yashsethu/PlaStick/CAD/Full Assembly - Part 1 (30).step

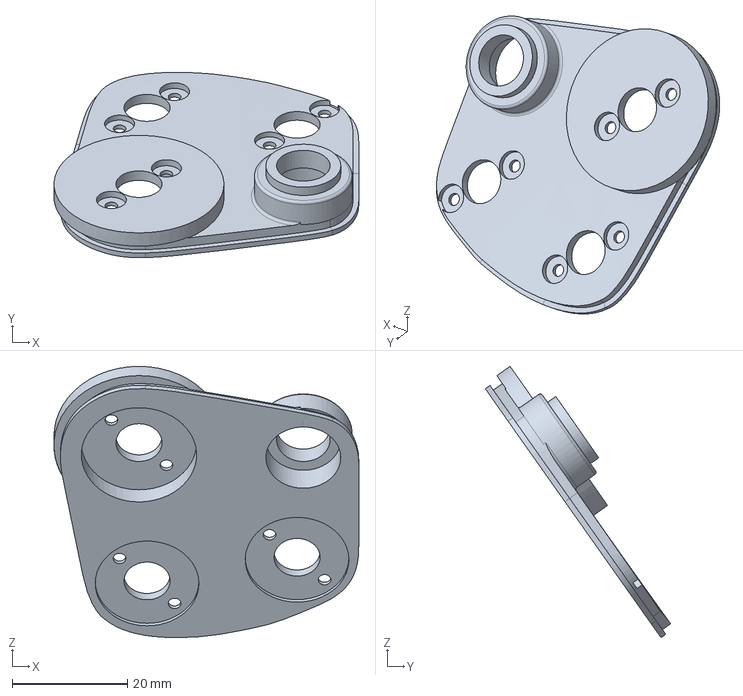
[picture p14: CAD file, 2025-06-24]
CAD/Full Assembly - Part 1 (30).step
52.9 x 32.2 x 47.1 mm
