yashsethu/PlaStick/CAD/Full Assembly - Part 1.step

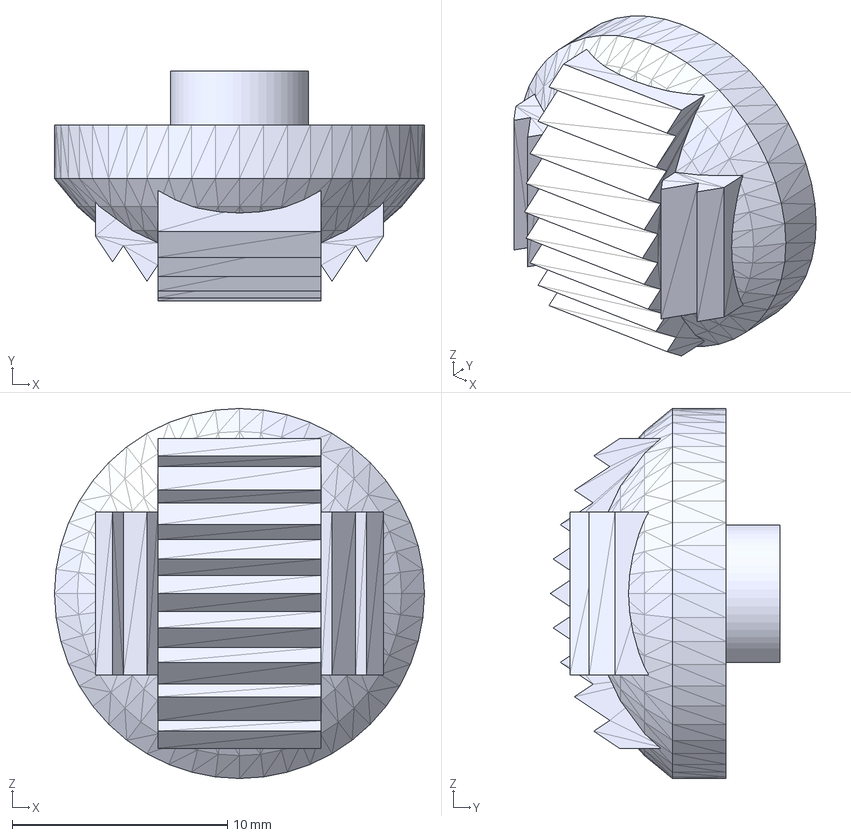
[picture p15: CAD file, 2025-06-24]
CAD/Full Assembly - Part 1.step
17.2 x 10.7 x 17.2 mm
