yashsethu/PlaStick/CAD/Full Assembly - p  BEARING, METRIC 600 MINIATURE SERIES, DOUBLE-SHIELDED  5mm ID × 11 OD × 3 W  —  685-ZZ.step

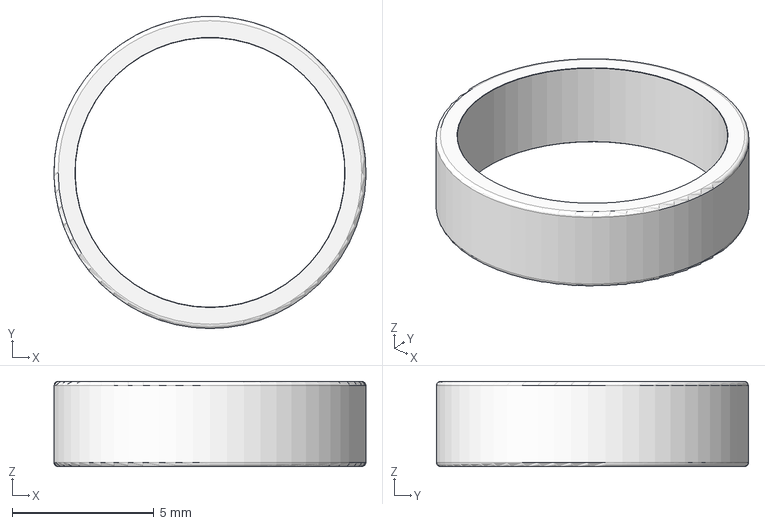
[picture p16: CAD file, 2025-06-24]
CAD/Full Assembly - p BEARING, METRIC 600 MINIATURE SERIES, DOUBLE-SHIELDED 5mm ID × 11 OD × 3 W — 685-ZZ.step
11.0 x 11.0 x 3.00 mm
