yashsethu/PlaStick/CAD/Full Assembly - Part 1 (26).step

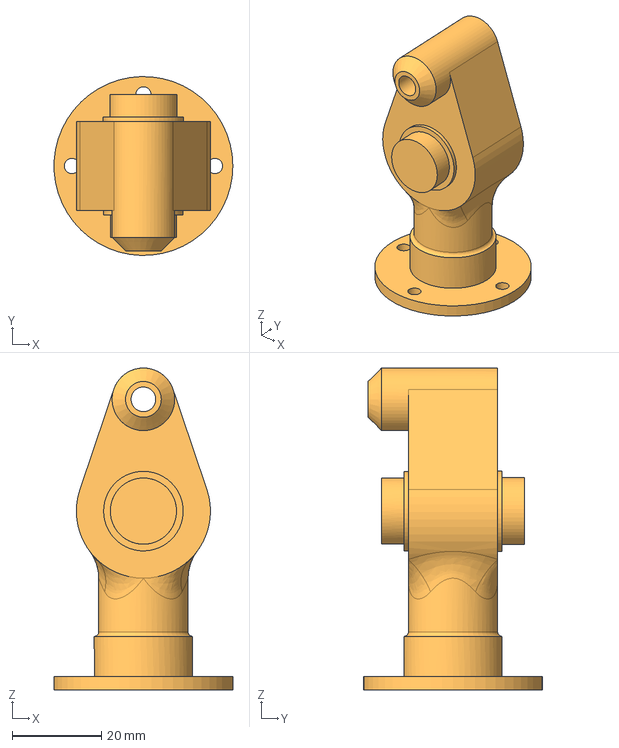
[picture p17: CAD file, 2025-06-24]
CAD/Full Assembly - Part 1 (26).step
40.0 x 40.0 x 72.0 mm
