yashsethu/PlaStick/CAD/Full Assembly - Part 6.step

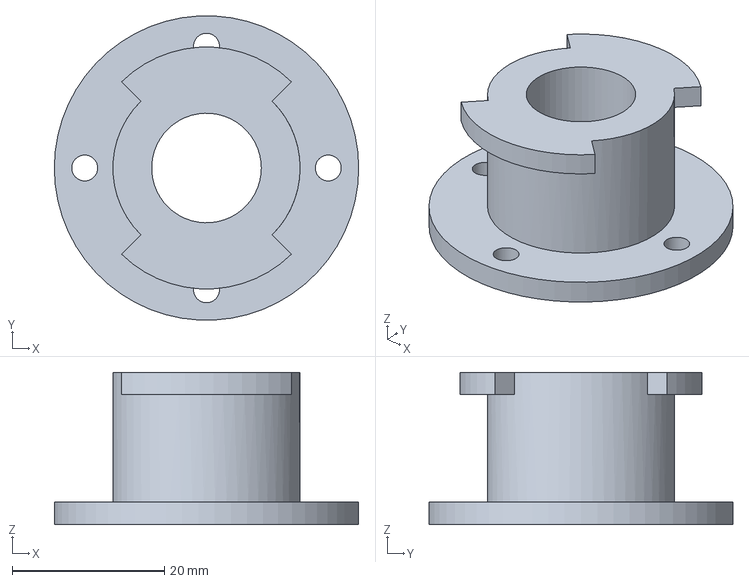
[picture p18: CAD file, 2025-06-24]
CAD/Full Assembly - Part 6.step
40.0 x 39.9 x 20.0 mm
