yashsethu/PlaStick/CAD/Full Assembly - Part 1 (44).step

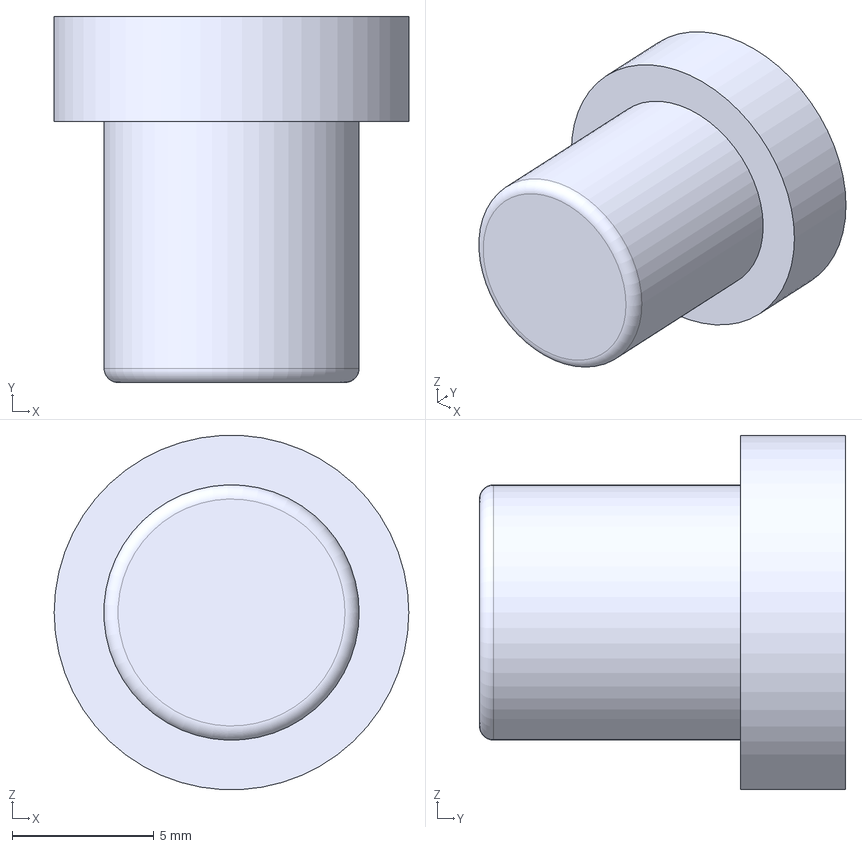
[picture p19: CAD file, 2025-06-24]
CAD/Full Assembly - Part 1 (44).step
12.5 x 12.9 x 12.5 mm
