yashsethu/PlaStick/CAD/Full Assembly - Part 1 (25).step

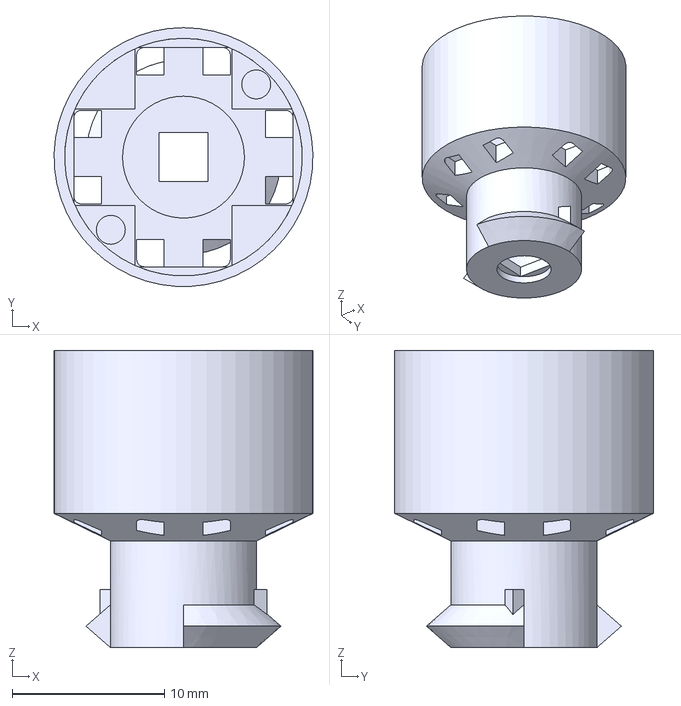
[picture p20: CAD file, 2025-06-24]
CAD/Full Assembly - Part 1 (25).step
17.0 x 17.0 x 19.5 mm
