yashsethu/PlaStick/CAD/Full Assembly - p  BEARING, METRIC 600 MINIATURE SERIES, DOUBLE-SHIELDED  5mm ID × 11 OD × 3 W  —  685-ZZ (11).step

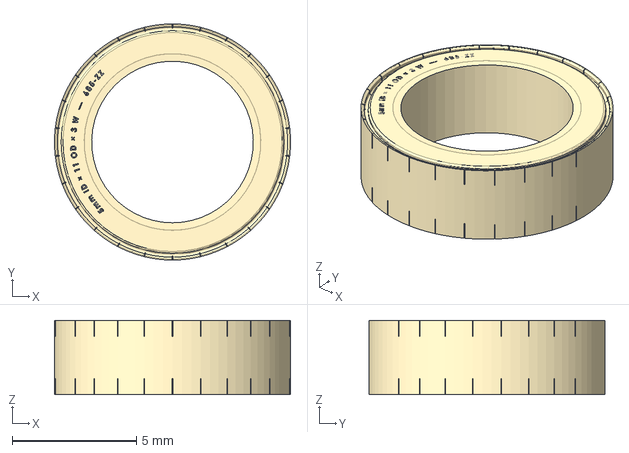
[picture p21: CAD file, 2025-06-24]
CAD/Full Assembly - p BEARING, METRIC 600 MINIATURE SERIES, DOUBLE-SHIELDED 5mm ID × 11 OD × 3 W — 685-ZZ (11).step
9.49 x 9.50 x 2.98 mm
