yashsethu/PlaStick/CAD/Full Assembly - Part 3.step

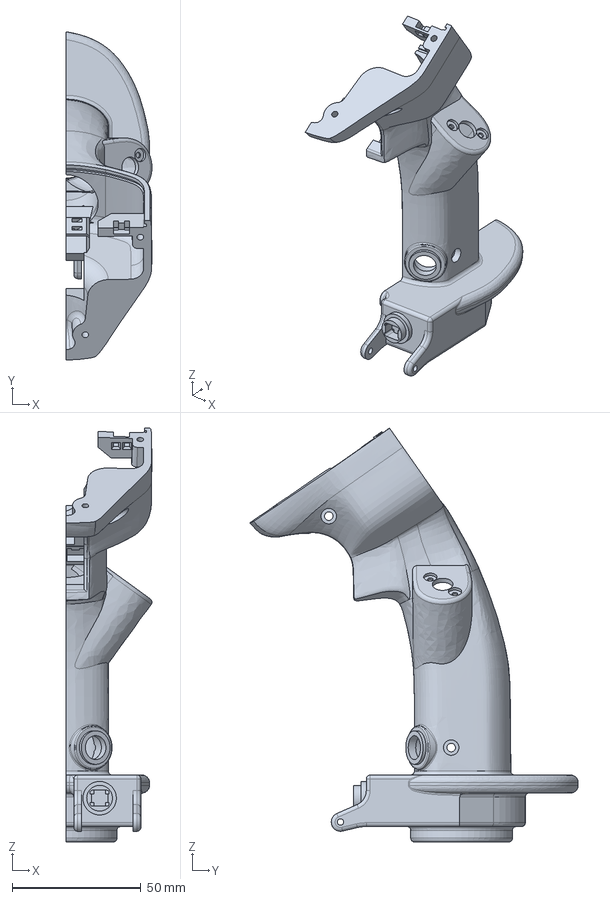
[picture p22: CAD file, 2025-06-24]
CAD/Full Assembly - Part 3.step
33.4 x 127.5 x 160.7 mm
