yashsethu/PlaStick/CAD/Full Assembly - Part 1 (32).step

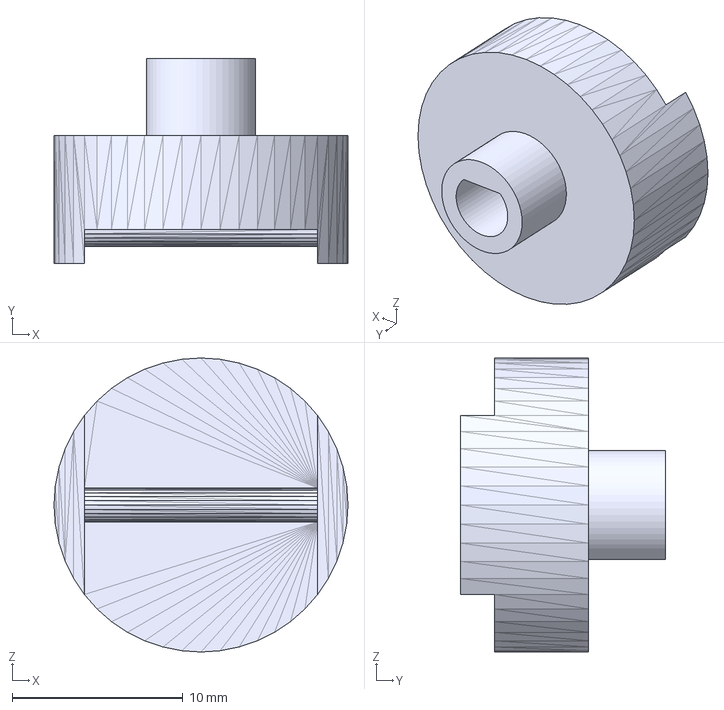
[picture p23: CAD file, 2025-06-24]
CAD/Full Assembly - Part 1 (32).step
17.2 x 12.0 x 17.2 mm
