yashsethu/PlaStick/CAD/Full Assembly - Part 1 (42).step

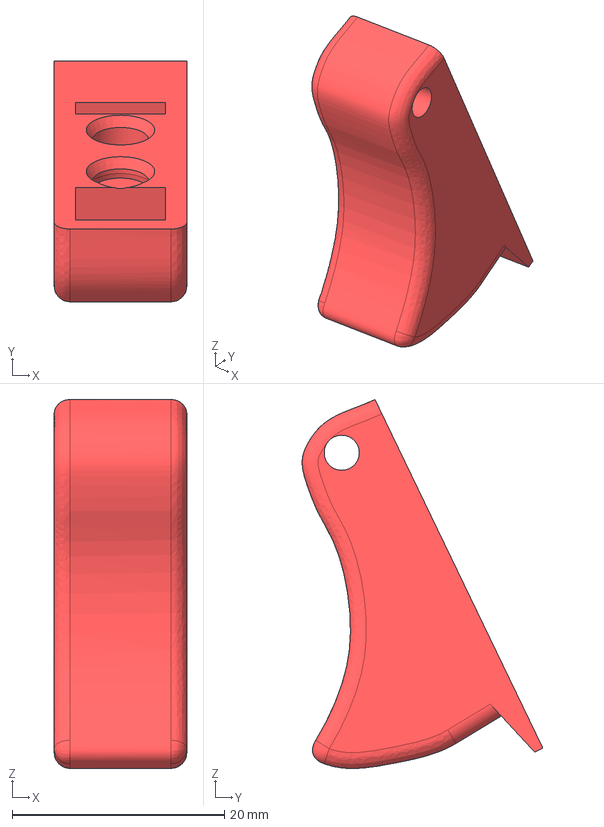
[picture p24: CAD file, 2025-06-24]
CAD/Full Assembly - Part 1 (42).step
12.5 x 22.7 x 34.8 mm
