yashsethu/PlaStick/CAD/Full Assembly - Part 5.step

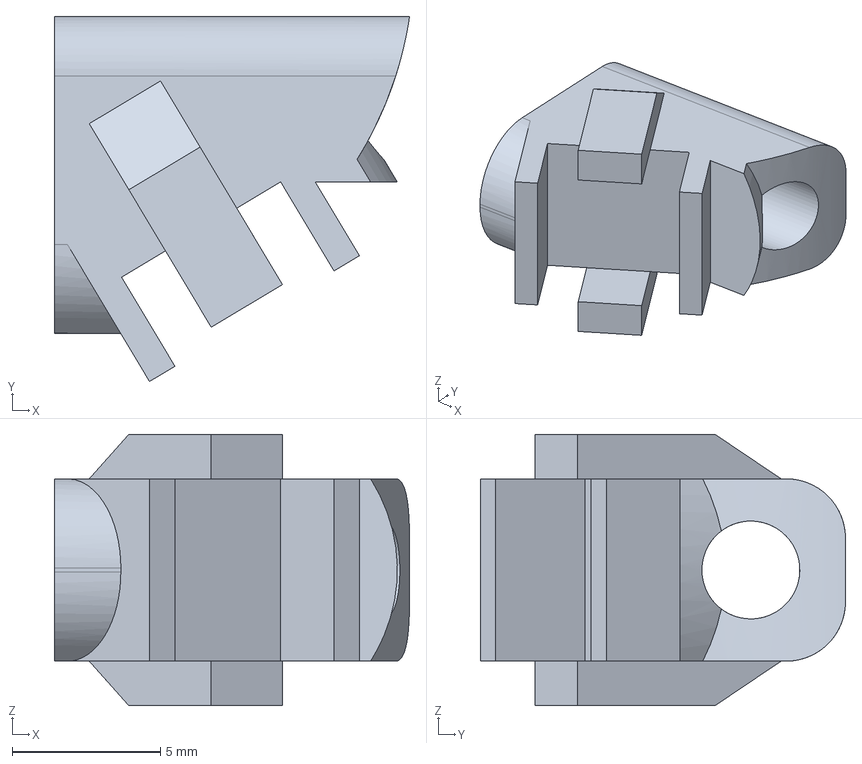
[picture p25: CAD file, 2025-06-24]
CAD/Full Assembly - Part 5.step
12.0 x 12.3 x 9.15 mm
