yashsethu/PlaStick/CAD/Full Assembly - Part 1 (43).step

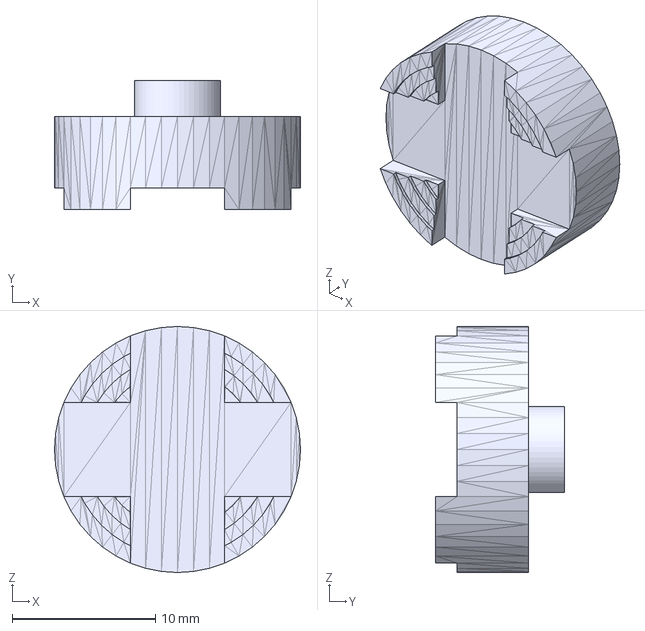
[picture p26: CAD file, 2025-06-24]
CAD/Full Assembly - Part 1 (43).step
17.2 x 9.00 x 17.2 mm
